mwalsh161/pirled/src/config/Config.h

#pragma once

#include <ArduinoOTA.h>
#include <ESP8266WebServer.h>
#include <stddef.h>
#include <stdint.h>

#include <array>

typedef uint8_t PirStates;

struct LedConfig {
    int16_t brightness;
    int16_t rampOnMs;
    uint32_t holdOnMs;
    int16_t rampOffMs;
    uint32_t waitOnMs;
    uint8_t pirMaskOn;
    uint8_t pirMaskOff;
};

struct Config {
    uint32_t magic;
    uint16_t version;

    int64_t timestamp;
    std::array<LedConfig, 4> ledConfig;

    uint32_t crc;
};

const Config& getConfig();
LedConfig& getLedConfig(size_t index);

bool saveConfig();  // Use with care to avoid eeprom wear.

class ConfigServer {
   public:
    ConfigServer();
    bool setup();
    PirStates pirOverrides() const { return m_pirOverrides; }
    void setPirOverrides(PirStates overrides) { m_pirOverrides = overrides; }

    void onWiFiConnected(const char* hostname);
    void onWiFiDisconnected();

    ~ConfigServer() { m_server.stop(); }
    void handle();

   private:
    ESP8266WebServer m_server;
    ArduinoOTAClass m_ota;
    bool m_storedConfigValid = false;
    bool m_initialized = false;
    PirStates m_pirOverrides = 0;
};
