mwalsh161/pirled/src/system/PersistentStorage.cpp

#include "system/PersistentStorage.h"

#include <EEPROM.h>

namespace {
bool s_initialized = false;
}

size_t persistentBootHistoryOffset() { return CONFIG_EEPROM_OFFSET + LEGACY_CONFIG_STORAGE_BYTES; }

size_t persistentStaticNetworkConfigOffset() {
    return persistentBootHistoryOffset() + BOOT_HISTORY_STORAGE_BYTES;
}

size_t persistentStorageSize() {
    return persistentStaticNetworkConfigOffset() + STATIC_NETWORK_CONFIG_STORAGE_BYTES;
}

bool beginPersistentStorage() {
    if (s_initialized) return true;
    EEPROM.begin(persistentStorageSize());
    s_initialized = true;
    return s_initialized;
}
